wileycousins/clockblock/firmware/src/include/DS3234/DS3234.cpp

// clockblock
// Copyright 2013 by Wiley Cousins, LLC.
// shared under the terms of the MIT License
//
// file: DS3234.cpp
// description: class for DS3234 real-time clock

#include "DS3234.h"

// can we build it? yes we can!
// parameters:
//   SPI channel (implement later when I've written an SPI library)
//   chip select port, chip select pin
//   reset port, reset pin
//   interrupt port, interrupt pin
DS3234::DS3234(StuPId *s, volatile uint8_t *csPo, uint8_t csPi, volatile uint8_t *rstPo, uint8_t rstPi, volatile uint8_t *intPo, uint8_t intPi) {
  // save this shit
  // SPI channel
  spi = s;
  // chip select pin
  csPort = csPo;
  csPin = csPi;
  // reset
  rstPort = rstPo;
  rstPin = rstPi;
  // interrupt
  intPort = intPo;
  intPin = intPi;
}

// initialization - sets pin modes and whatnot
// returns false if osc has stopped, true otherwise (true means the RTC has a good time)
void DS3234::init() {
  // sets chip select pin to output and pulls it high
  // DDR is PORT - 1
  *(csPort-1) |= (1 << csPin);
  *csPort |= (1 << csPin);
  // do the same for the reset pin
  *(rstPort-1) |= (1 << rstPin);
  *rstPort |= (1 << rstPin);
  // ensure interrupt pin is set to an input
  *(intPort-1) &= ~(1 << intPin);

  // set up SPI
  spi->disable();
  // DS3234 is MSB first
  spi->setDataOrder(SPI_MSB_FIRST);
  // runs at up to 4MHz. dividing clock by 4 will ensure this isn't exceeded
  spi->setDataRate(SPI_DIV_4, SPI_SPEED_NORMAL);
  // supports SPI modes 1 and 3 (autodetects). let's use 3 (CPOL = 1, CPHA = 0)
  spi->setDataMode(3);
  // enable
  spi->enable();
}

bool DS3234::hasLostTime() {
  uint8_t stat;
  readReg(DS3234_CTRL_STAT, 1, &stat);
  return (stat & DS3234_OSF);
}

// enable the square wave output on the INT/SQW pin at given mode
//  - 0 : 1 Hz
//  - 1 : 1.024 kHz
//  - 2 : 4.096 kHz
//  - 3 : 8.192 kHz
void DS3234::enableSquareWave(uint8_t mode) {
  uint8_t c;
  readReg(DS3234_CTRL, 1, &c);
  // clear the rate select bits and the int enable bit (enabling squarewave)
  c &= ~( DS3234_INTCN | DS3234_RS2 | DS3234_RS1 );
  // set the new rate bits (bits 3 and 4)
  c |= ( (mode & 3) << 3 );
  writeReg(DS3234_CTRL, 1, &c);
}

void DS3234::enableAlarm(uint8_t alarms) {
  // set the int enable bit
  uint8_t c;
  readReg(DS3234_CTRL, 1, &c);
  c |= DS3234_INTCN;
  writeReg(DS3234_CTRL, 1, &c);
}

// set and get time
// array format is { sec, min, hr }
// AM = 0, PM = 1
// setter will either change array to properly coded data or set bad inputs to 255 and return false
// 24-hour mode
bool DS3234::setTime(uint8_t *tm) {
  // check our inputs
  bool badInput = false;
  if (tm[2] > 23) {
    badInput = true;
    tm[2] = 255;
  }
  if (tm[1] > 59) {
    badInput = true;
    tm[1] = 255;
  }
  if (tm[0] > 59) {
    badInput = true;
    tm[0] = 255;
  }
  if (badInput) {
    return false;
  }

  // encode the time properly
  // hours
  tm[2] = ( ((tm[2]/10) << 4) | (tm[2]%10) );
  // minutes
  tm[1] = ( ((tm[1]/10) << 4) | (tm[1]%10) );
  // seconds
  tm[0] = ( ((tm[0]/10) << 4) | (tm[0]%10) );

  // transfer the time in
  writeReg(DS3234_SEC, 3, tm);

  // clear the osc stop flag
  uint8_t c;
  readReg(DS3234_CTRL_STAT, 1, &c);
  c &= ~DS3234_OSF;
  writeReg(DS3234_CTRL_STAT, 1, &c);

  return true;
}

// 12-hour mode
bool DS3234::setTime(uint8_t ampm, uint8_t *tm) {
  // check our inputs
  bool badInput = false;
  if (tm[2] < 1 || tm[2] > 12) {
    badInput = true;
    tm[2] = 255;
  }
  if (tm[1] > 59) {
    badInput = true;
    tm[1] = 255;
  }
  if (tm[0] > 59) {
    badInput = true;
    tm[0] = 255;
  }
  if (ampm != DS3234_AM && ampm != DS3234_PM) {
    badInput = true;
  }
  if (badInput) {
    return false;
  }

  // encode the time properly
  // hours
  tm[2] = ( DS3234_12_HOUR | ampm | ((tm[2]/10) << 4) | (tm[2]%10) );
  // minutes
  tm[1] = ( ((tm[1]/10) << 4) | (tm[1]%10) );
  // seconds
  tm[0] = ( ((tm[0]/10) << 4) | (tm[0]%10) );

  // transfer the time in
  writeReg(DS3234_SEC, 3, tm);

  // clear the osc stop flag
  uint8_t c;
  readReg(DS3234_CTRL_STAT, 1, &c);
  c &= ~(1<<7);
  writeReg(DS3234_CTRL_STAT, 1, &c);\

  return true;
}

// getter returns 0 if AM or in 24 hour mode, DS3234_PM if in 12-hour mode and it's PM
uint8_t DS3234::getTime(uint8_t *tm) {
  uint8_t ret = 0;
  // get the data
  readReg(DS3234_SEC, 3, tm);

  // decode the data
  // hours
  // 12-hour mode
  if ( tm[2] & DS3234_12_HOUR ) {
    ret = tm[2] & DS3234_PM;
    tm[2] = (((tm[2]>>4) & 1) * 10) + (tm[2] & 0x0F);
  }
  // else, 24-hour mode
  else {
    ret = 0;
    tm[2] = ((tm[2]>>4) * 10) + (tm[2] & 0x0F);
  }
  // minutes
  tm[1] = ((tm[1] >> 4) * 10) + (tm[1] & 0x0F);
  // seconds
  tm[0] = ((tm[0] >> 4) * 10) + (tm[0] & 0x0F);

  return ret;
}

// SPI helpers
// start / end
// ensures SPI options are set correctly and pulls the chip select line low / high to start / end a transfer
void DS3234::spiStart() {
  // pull the chip select line low to begin the transfer
  *csPort &= ~(1 << csPin);
}

void DS3234::spiEnd() {
  // pull the chip select line high to end the transfer
  *csPort |= (1 << csPin);
}

// read / write
// parameters:
//   register address to start at
//   number of bytes to transfer
//   buffer to read to / write from
uint8_t DS3234::readSingleReg(uint8_t reg) {
  uint8_t data;
  spiStart();
  spi->transfer(reg);
  data = spi->transfer(0);
  spiEnd();
  return data;
}

void DS3234::readReg(uint8_t reg, uint8_t n, uint8_t *data) {
  spiStart();
  spi->transfer(reg);
  for (uint8_t i=0; i<n; i++) {
    data[i] = spi->transfer(0);
  }
  spiEnd();
}

void DS3234::writeReg(uint8_t reg, uint8_t n, uint8_t *data) {
  spiStart();
  spi->transfer(DS3234_SPI_WRITE | reg);
  for (uint8_t i=0; i<n; i++) {
    spi->transfer(data[i]);
  }
  spiEnd();
}
