wileycousins/clockblock/firmware/src/input.h

// clockblock
// Copyright 2013 by Wiley Cousins, LLC.
// shared under the terms of the MIT License
//
// file: input.h
// description: header file for the clockblock user input class

#ifndef CLOCKBLOCK_INPUT_H
#define CLOCKBLOCK_INPUT_H

// typedefs
#include <stdint.h>

#define INPUT_DEBOUNCE_COUNT  3
#define INPUT_HOLD_COUNT      30
#define INPUT_REPEAT_COUNT    20

class Input {
public:
  // contructor - gives private variables default values
  Input(void);

  // get the flag states and clear as necessary
  bool getPress(uint8_t *s);
  // handle debouncing
  void handleTimer(void);
    // interrupt helpers
  void enableTimer(void);
  void disableTimer(void);

  // initialization
  void init(void);

private:
  // get switch state
  uint8_t getState(void);

  // init switch pins as inputs
  void initPins(void);
  // init timer for debouncing
  void initTimer(void);

  // ISR volatiles
  // switch states
  volatile uint8_t state;
  volatile uint8_t pressState;
  // switch timer counter
  volatile uint8_t timerCount;
  // switch event flags
  volatile bool release;
  volatile bool press;
};

#endif
